LeafCutterLabs/nope1/software/QMK/nope1/keymaps/vial/keymap.c

/* Copyright 2018 Yiancar
 *
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
 * You should have received a copy of the GNU General Public License
 * along with this program.  If not, see <http://www.gnu.org/licenses/>.
 */
#include QMK_KEYBOARD_H

extern MidiDevice midi_device;

enum custom_keycodes {
    MIDI_CC20 = SAFE_RANGE,
	MIDI_CC21,
	MIDI_CC22,
	MIDI_CC23,
	MIDI_CC24,
	MIDI_CC25,
	MIDI_CC26,
	MIDI_CC85,
	MIDI_CC86,
	MIDI_CC88,
	MIDI_CC89,
	MIDI_CC90,
	MIDI_CC102,  
	MIDI_CC103,
	MIDI_CC104,
	MIDI_CC105,
	MIDI_CC106,
	MIDI_CC107,
	MIDI_CC108,
	MIDI_CC109,
	MIDI_CC110,
	MIDI_CC111,
	MIDI_CC112,
	MIDI_CC117,
	MIDI_CC118,
	MIDI_CC119,
};

#define MIDI_CC_OFF 0
#define MIDI_CC_ON  127

bool process_record_user(uint16_t keycode, keyrecord_t *record) {
    switch (keycode) {
        case MIDI_CC20:
            if (record->event.pressed) {
                midi_send_cc(&midi_device, midi_config.channel, 20, MIDI_CC_ON);
            } else {
                midi_send_cc(&midi_device, midi_config.channel, 20, MIDI_CC_OFF);
            }
            return true;
		case MIDI_CC21:
            if (record->event.pressed) {
                midi_send_cc(&midi_device, midi_config.channel, 21, MIDI_CC_ON);
            } else {
                midi_send_cc(&midi_device, midi_config.channel, 21, MIDI_CC_OFF);
            }
            return true;
		case MIDI_CC22:
            if (record->event.pressed) {
                midi_send_cc(&midi_device, midi_config.channel, 22, MIDI_CC_ON);
            } else {
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
  MI_F3,		MI_Ab3,		MI_Bb3, 	MI_Db4, 	MI_Eb4,		MI_Gb4,		MI_Ab4,		MI_Bb4,		MI_Db5,		MI_Eb5,
  MI_F3,		MI_F3,		MI_G3,  	MI_A3,  	MI_B3,  	MI_C4,  	MI_D4,  	MI_E4,  	MI_F4,  	MI_G4
  ),
};

void matrix_init_user(void) {

}

void matrix_scan_user(void) {

}

void led_set_user(uint8_t usb_led) {

}
/*
void housekeeping_task_user(void) { 
    rgblight_setrgb_at(RGB_ORANGE, 0);
    rgblight_setrgb_at(RGB_WHITE, 18);
	rgblight_setrgb_at(RGB_PURPLE, 19);
    rgblight_setrgb_at(RGB_PINK, 37);
	rgblight_setrgb_at(RGB_ORANGE, 38);
    rgblight_setrgb_at(RGB_WHITE, 56);
	
}
*/
#if defined(ENCODER_MAP_ENABLE)
const uint16_t PROGMEM encoder_map[][NUM_ENCODERS][2] = {
    [0] = { ENCODER_CCW_CW(KC_1, KC_2), ENCODER_CCW_CW(KC_3, KC_4), ENCODER_CCW_CW(KC_5, KC_6), ENCODER_CCW_CW(KC_7, KC_8) },
};
#endif

//midi_send_cc(&midi_device, midi_config.channel, 80, 30);
